reyanshsolis/inertial_odometry/Results/ekf_madgwick/01.png

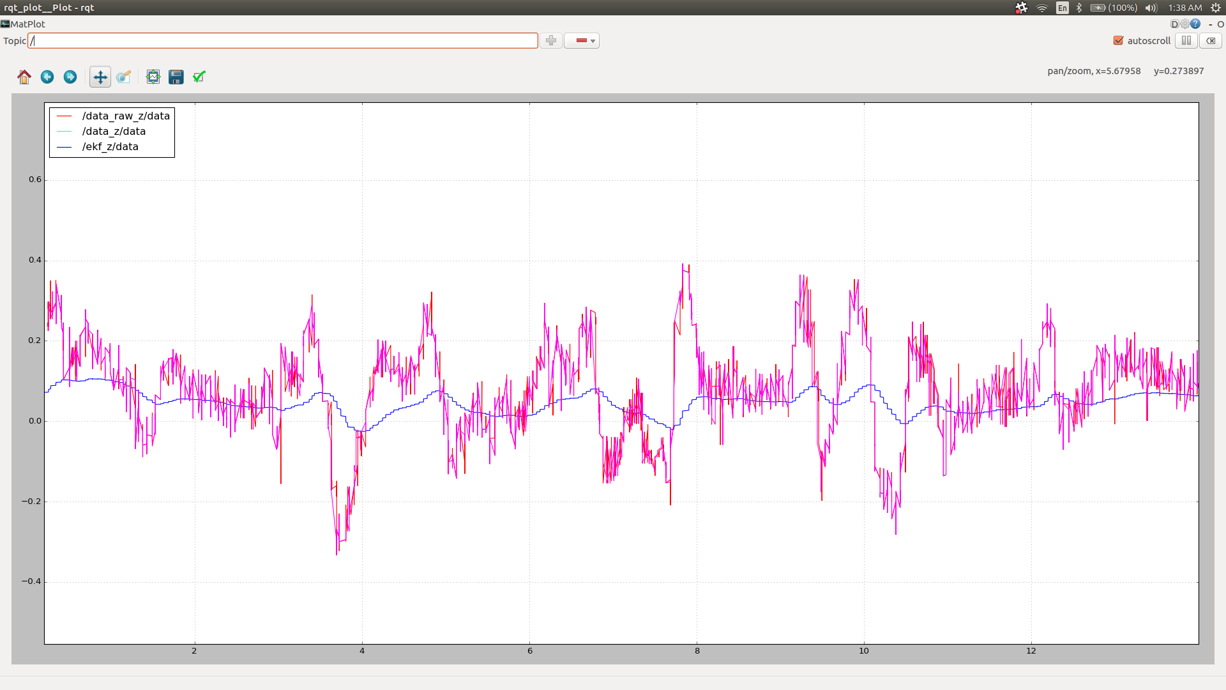
Results/ekf_madgwick/01.png
