reyanshsolis/inertial_odometry/Results/ekf_madgwick/2.png

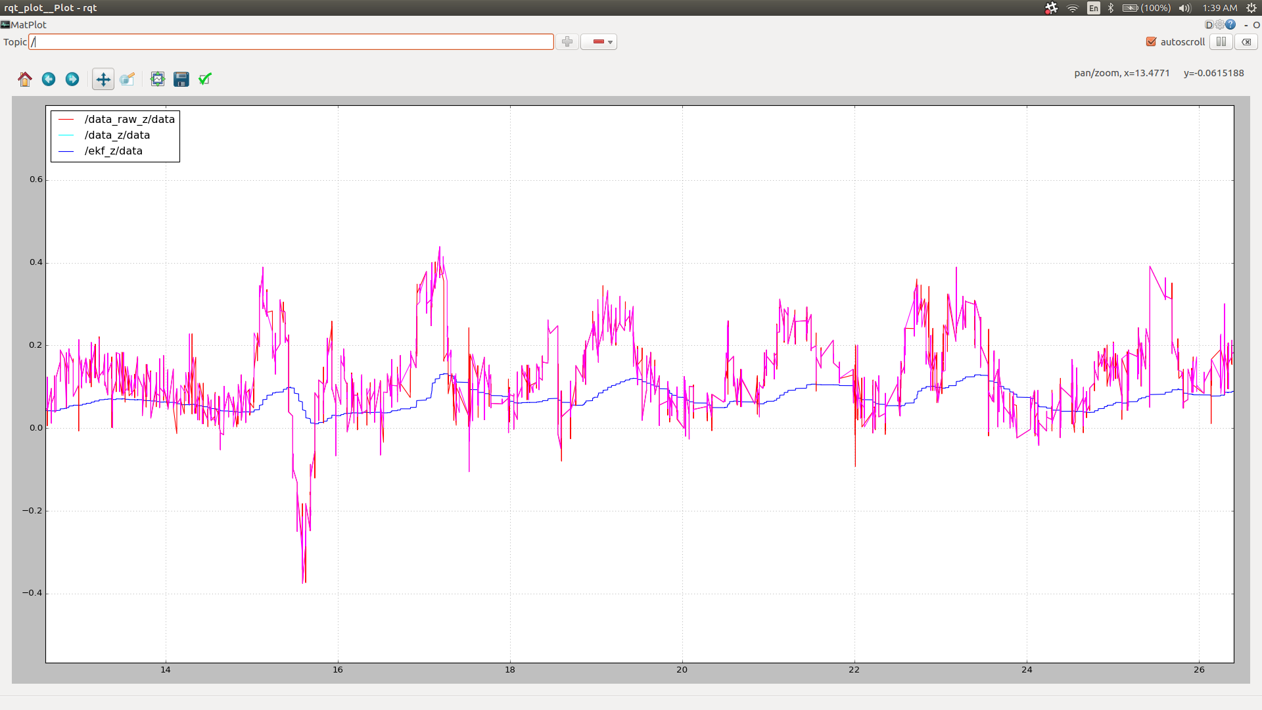
Results/ekf_madgwick/2.png
