reyanshsolis/inertial_odometry/Results/ekf_madgwick/3.png

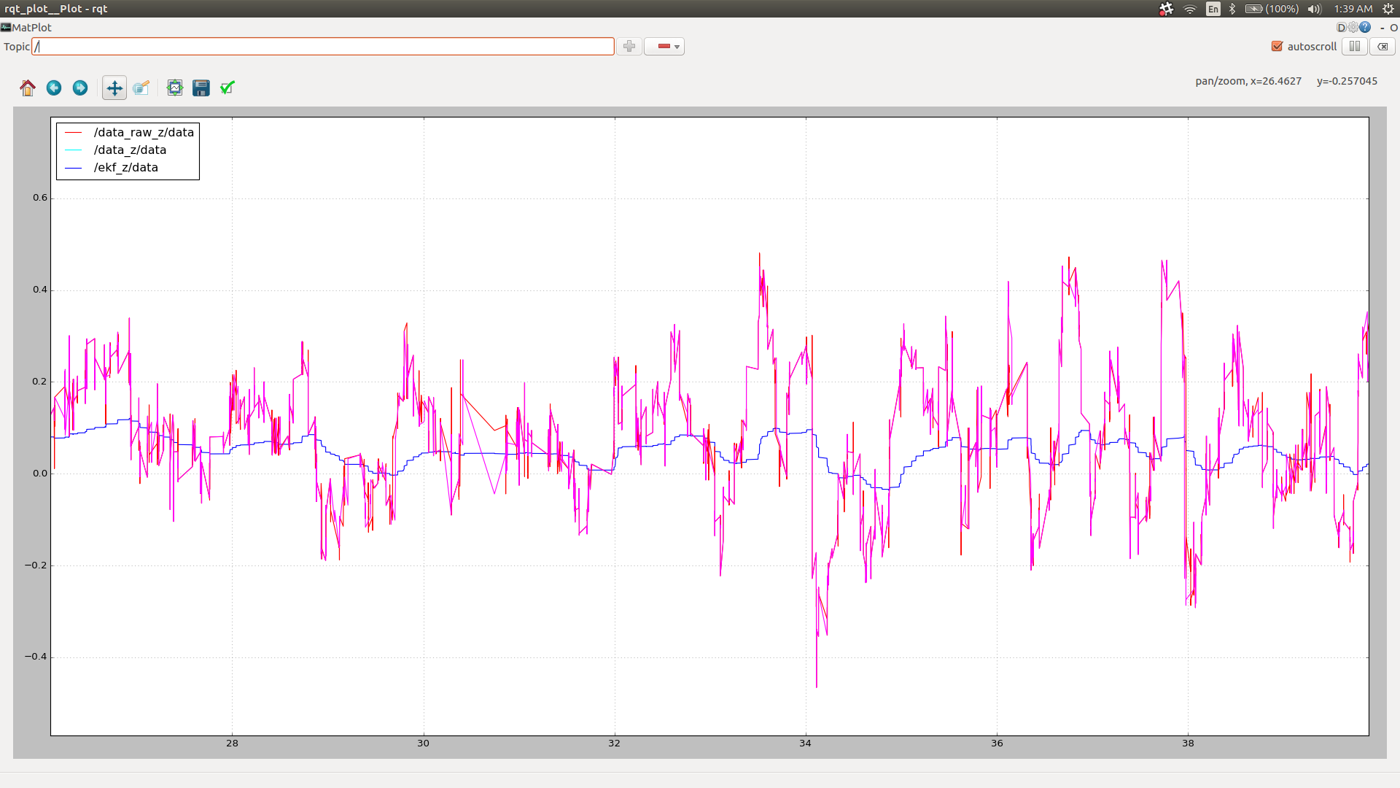
Results/ekf_madgwick/3.png
