reyanshsolis/inertial_odometry/Results/ekf_madgwick/4.png

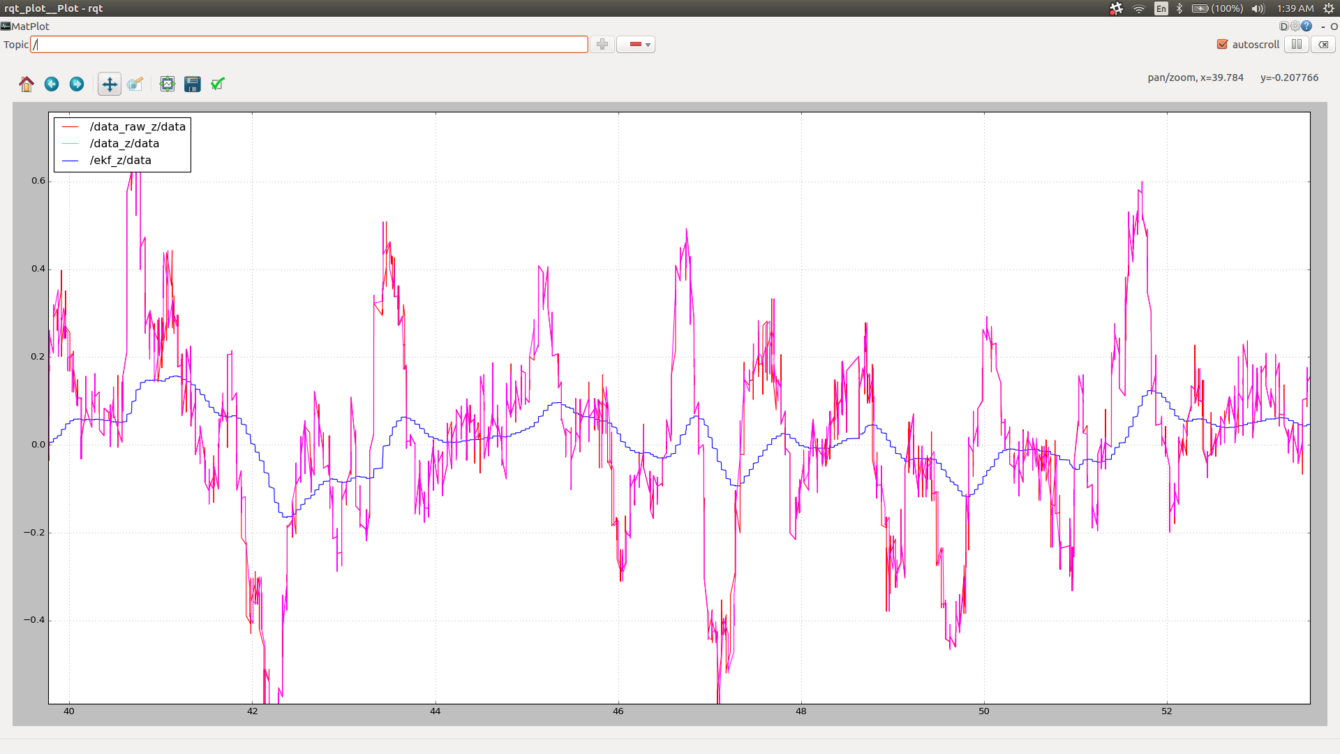
Results/ekf_madgwick/4.png
