reyanshsolis/inertial_odometry/Results/ekf_madgwick/6.png

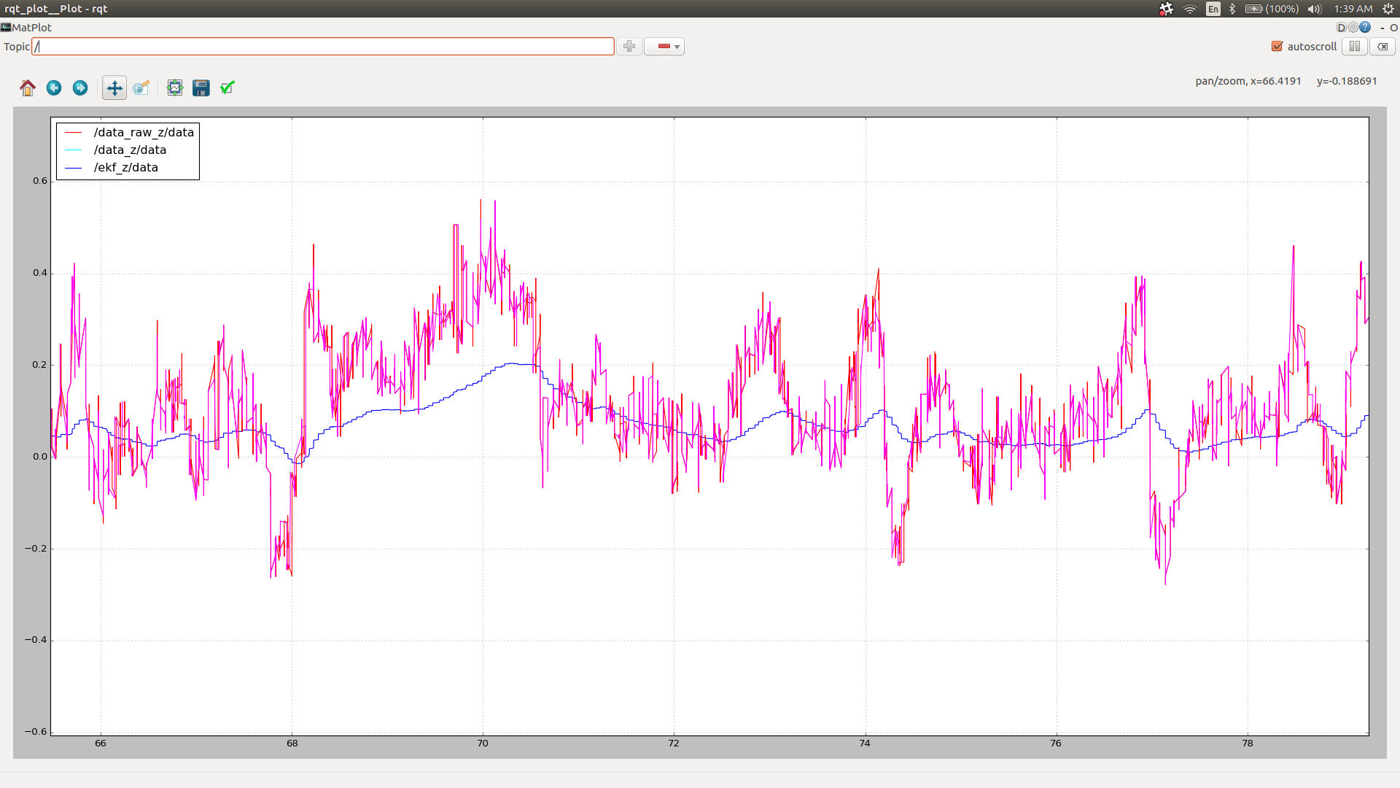
Results/ekf_madgwick/6.png
