reyanshsolis/inertial_odometry/Results/ekf_madgwick/7.png

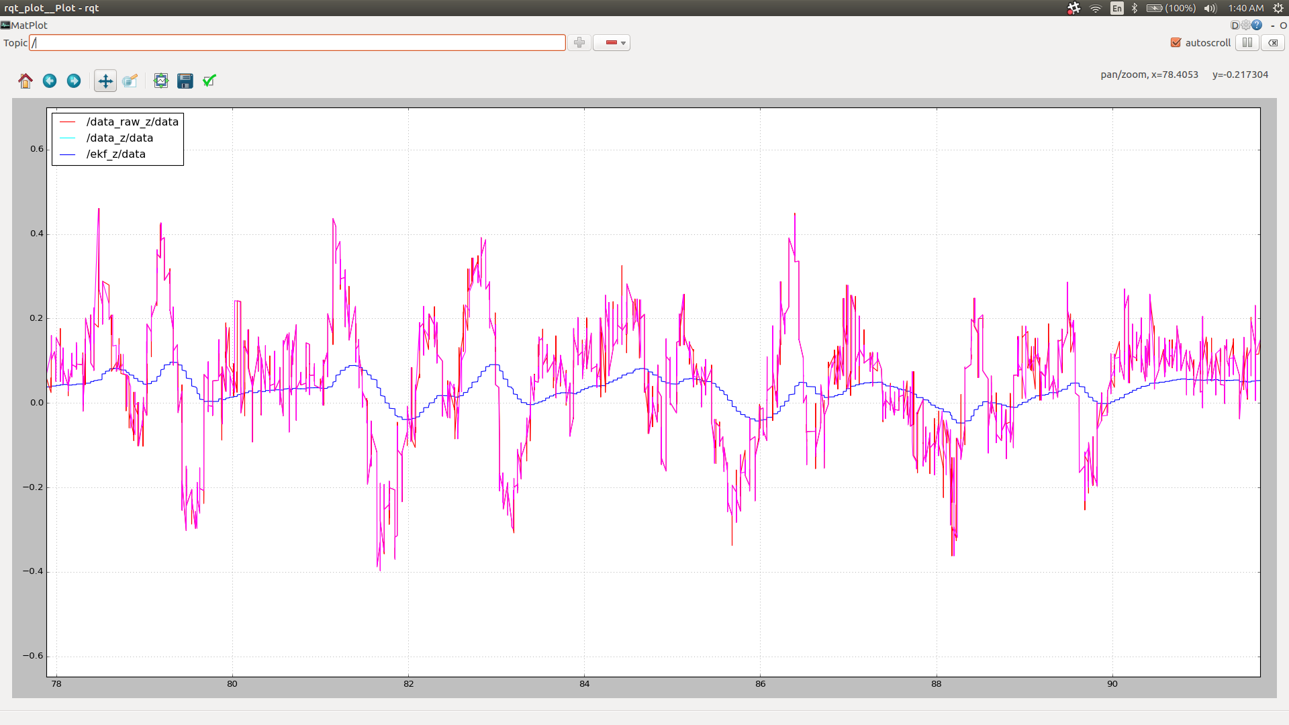
Results/ekf_madgwick/7.png
