reyanshsolis/inertial_odometry/Results/ekf_madgwick/8.png

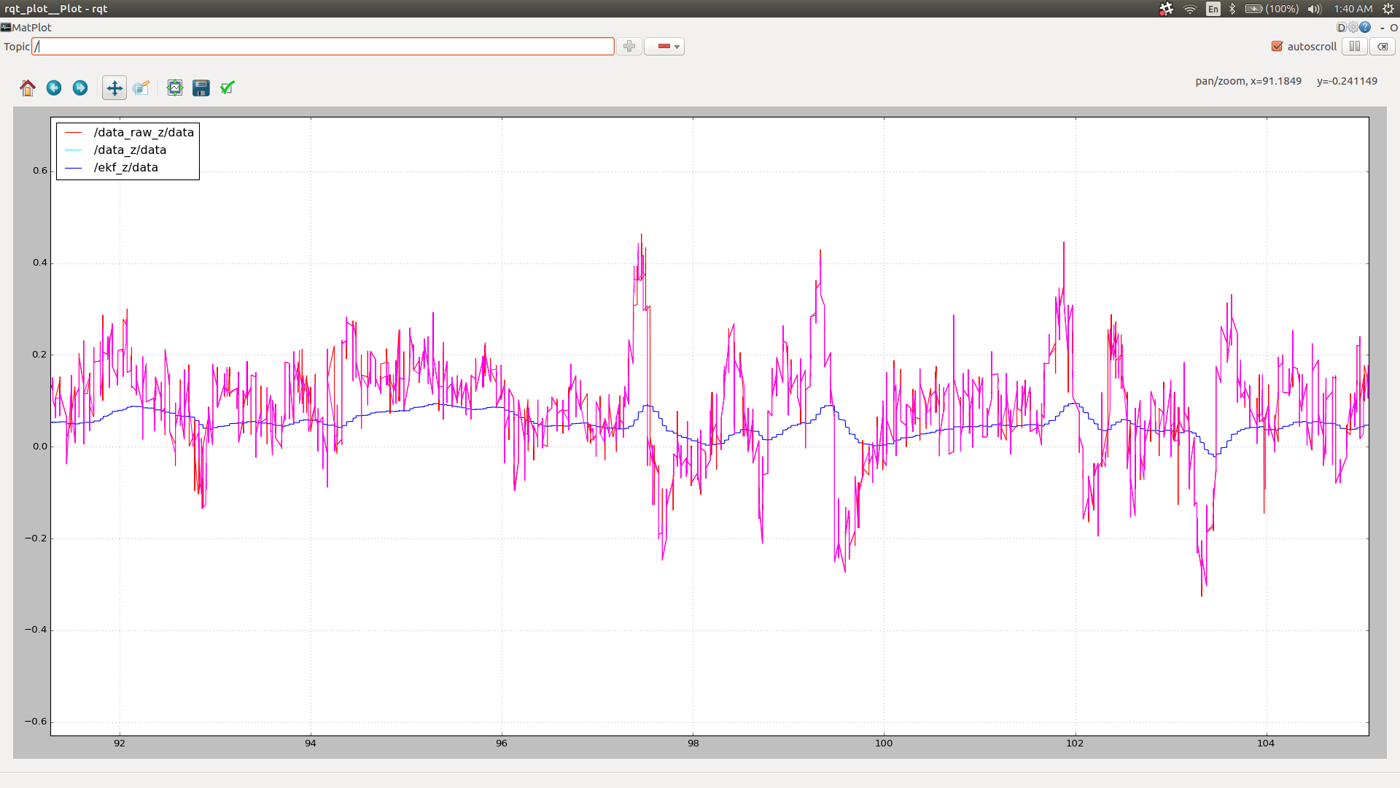
Results/ekf_madgwick/8.png
