reyanshsolis/inertial_odometry/Results/ekf_madgwick/9.png

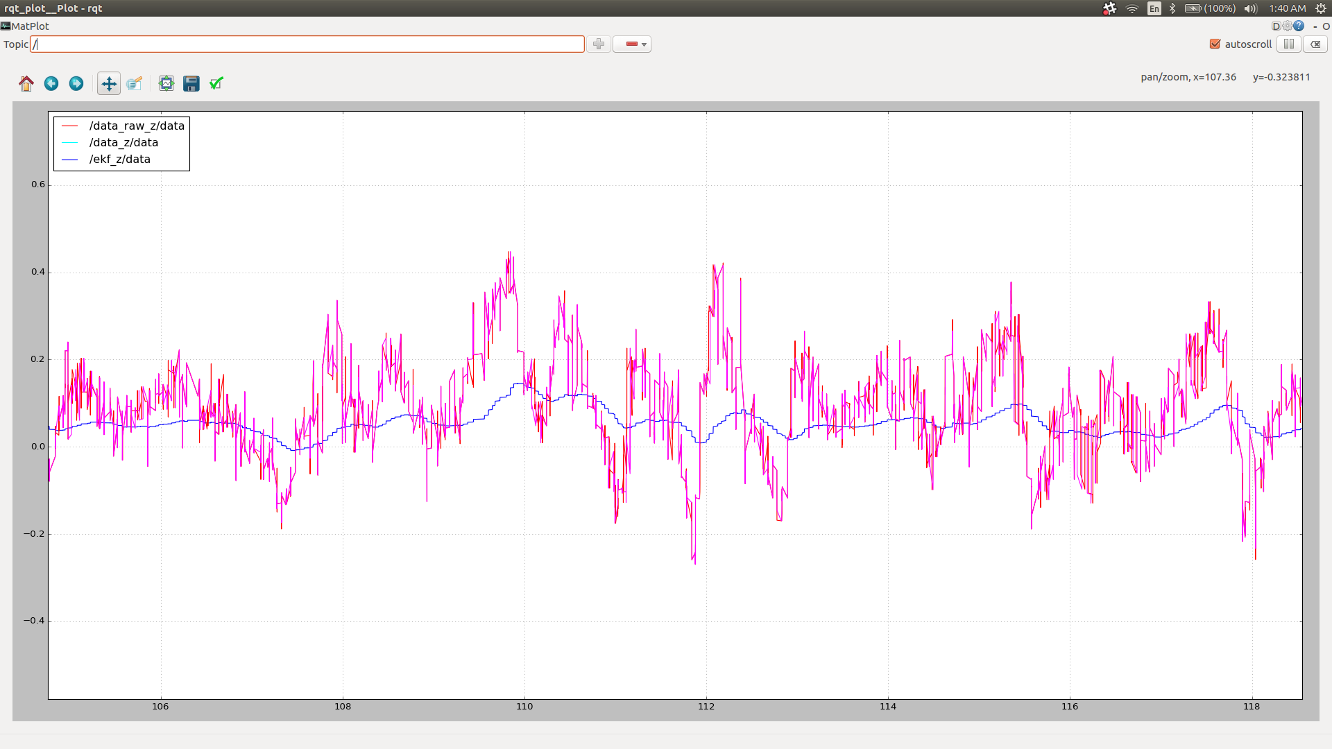
Results/ekf_madgwick/9.png
