reyanshsolis/inertial_odometry/Results/ekf_madgwick/10.png

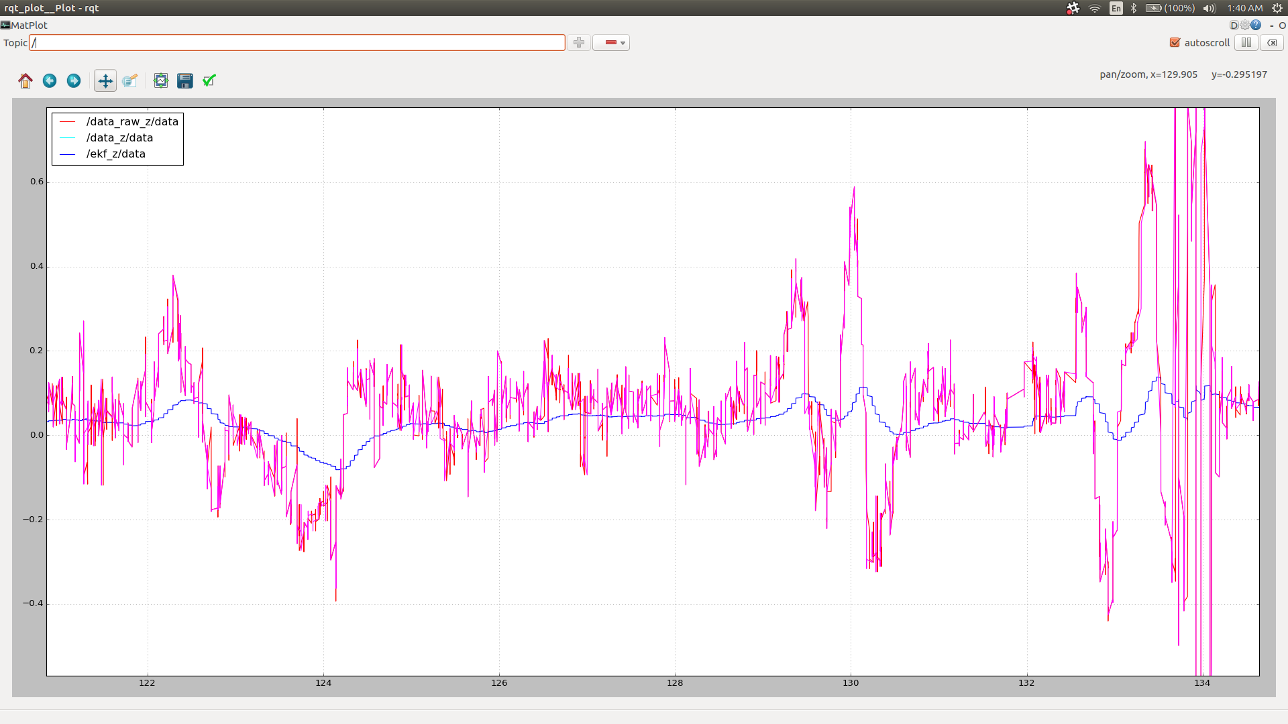
Results/ekf_madgwick/10.png
