reyanshsolis/inertial_odometry/Results/ekf_madgwick/issue_01_lag.png

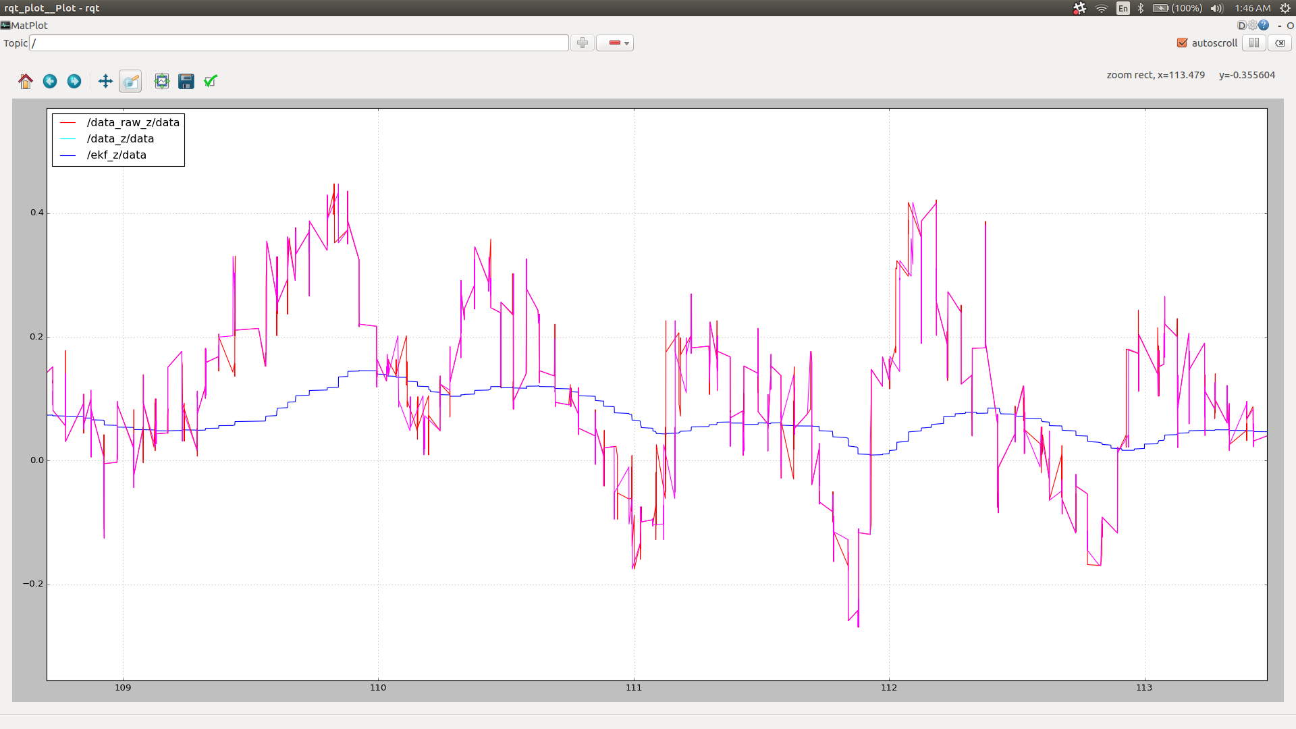
Results/ekf_madgwick/issue_01_lag.png
